TENNLab-UTK/neuropong/models/pcb_case/Case_enclosure.jpg

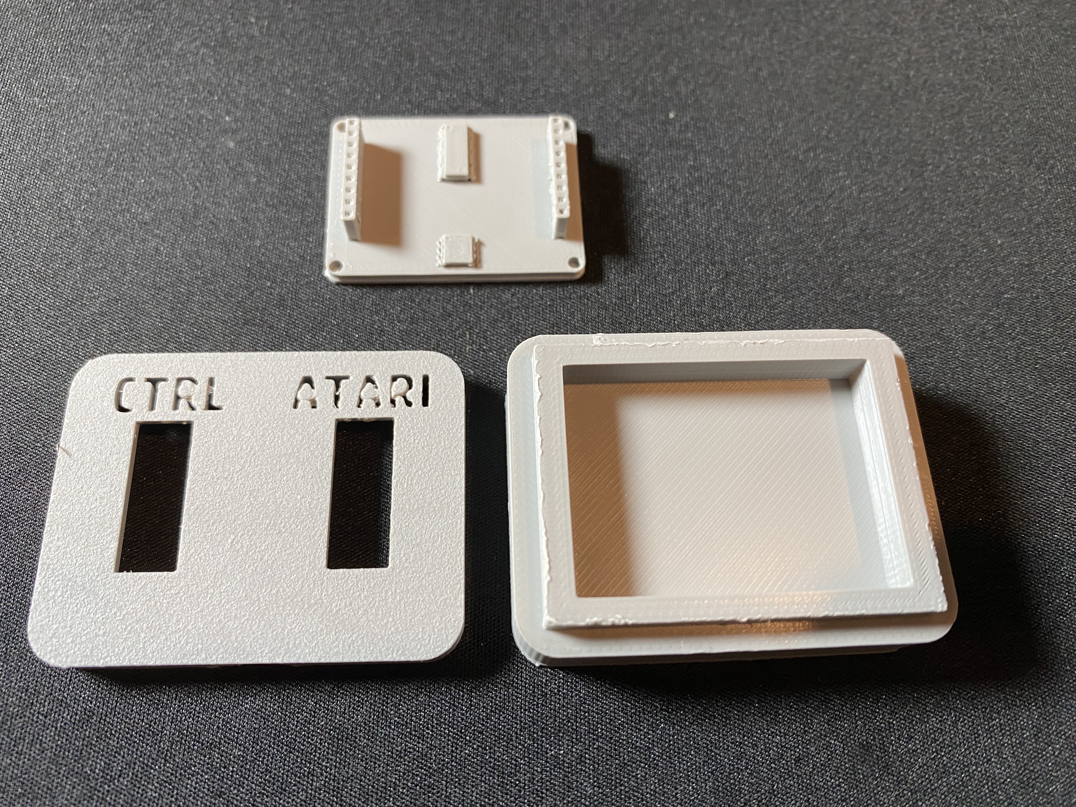
models/pcb_case/Case_enclosure.jpg
