TENNLab-UTK/neuropong/models/pcb_case/pcb dim.png

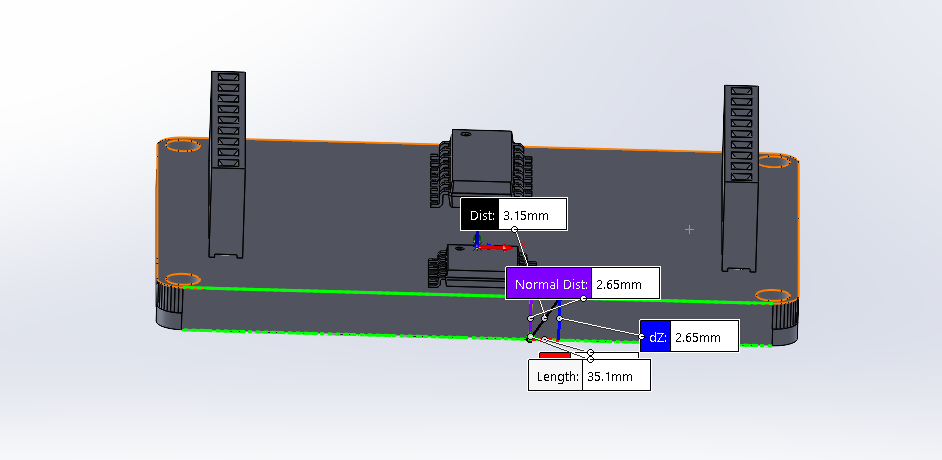
models/pcb_case/pcb dim.png
